qha/community-core/stl-export-v27/Cylinder.stl

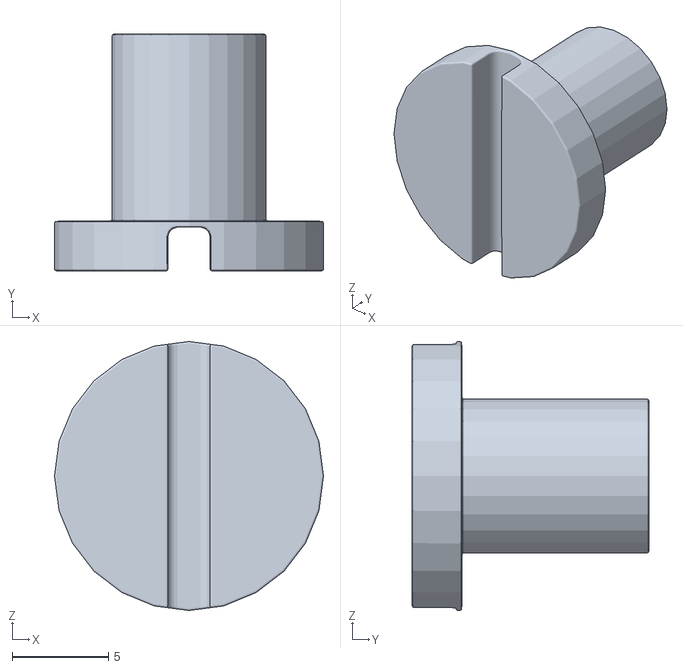
[picture p23: CAD file, 2021-09-25, an earlier design]
stl-export-v27/Cylinder.stl
14.0 x 12.3 x 14.0
